Amperstrand/nucula-enclosure/output/renders/detail_keypad_bay.png

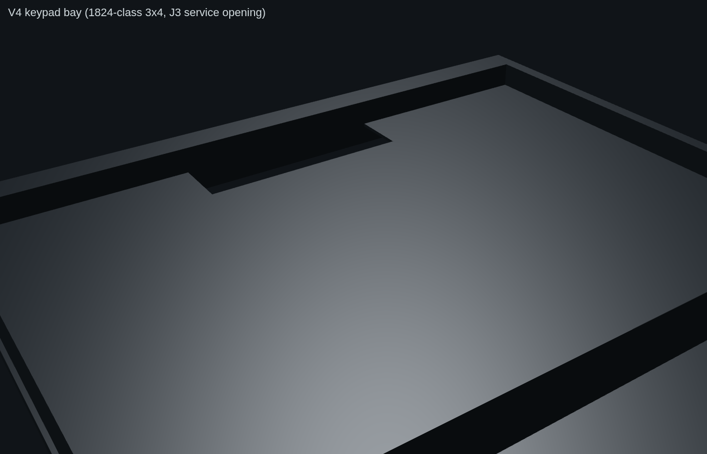
output/renders/detail_keypad_bay.png
