Amperstrand/nucula-enclosure/output/renders/detail_button_ports.png

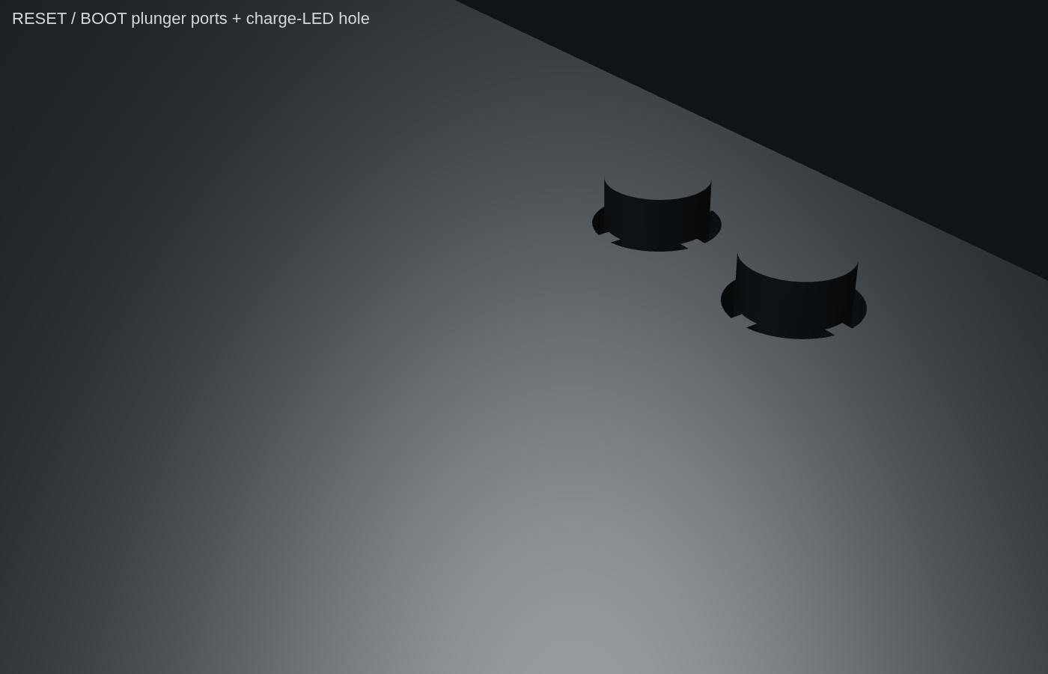
output/renders/detail_button_ports.png
