Amperstrand/nucula-enclosure/output/renders/detail_battery_pocket.png

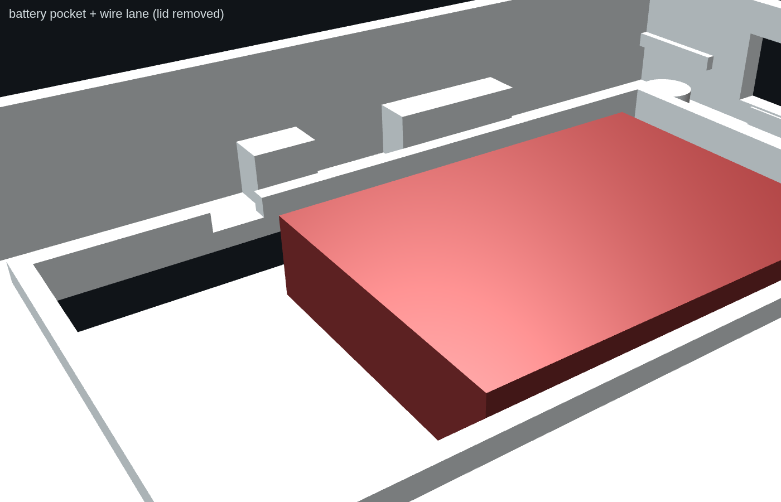
output/renders/detail_battery_pocket.png
