Amperstrand/nucula-enclosure/output/renders/detail_coupon.png

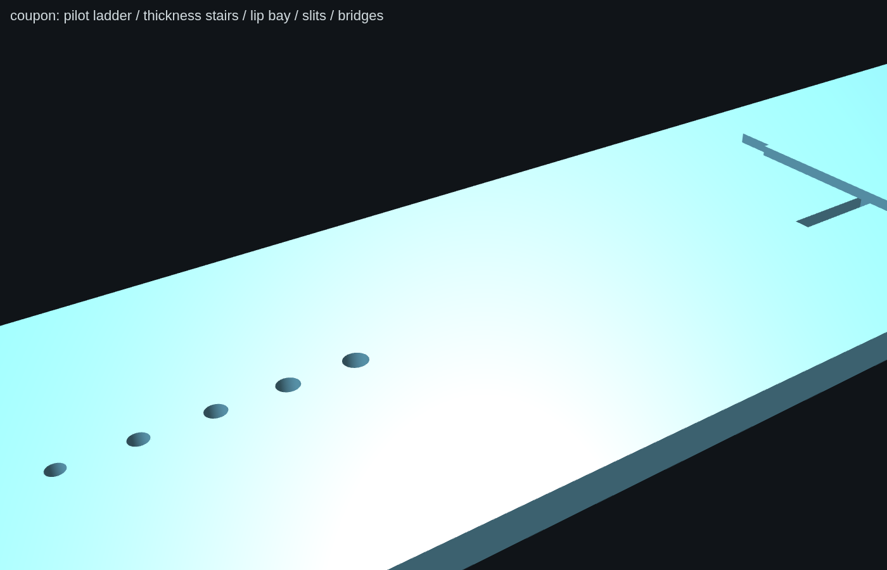
output/renders/detail_coupon.png
