Amperstrand/nucula-enclosure/output/renders/detail_popout_window.png

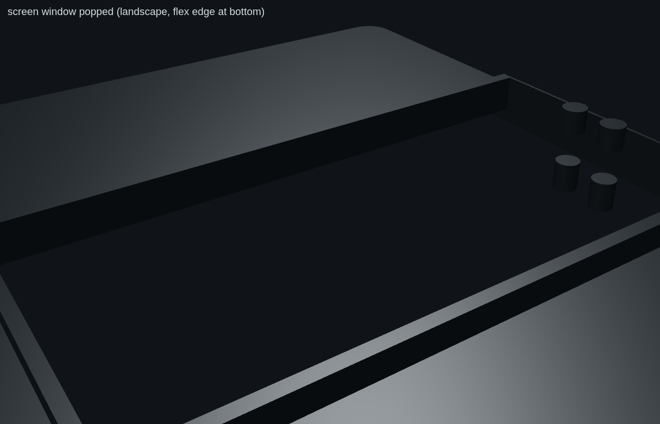
output/renders/detail_popout_window.png
