Amperstrand/nucula-enclosure/output/renders/detail_usb_battery_ports.png

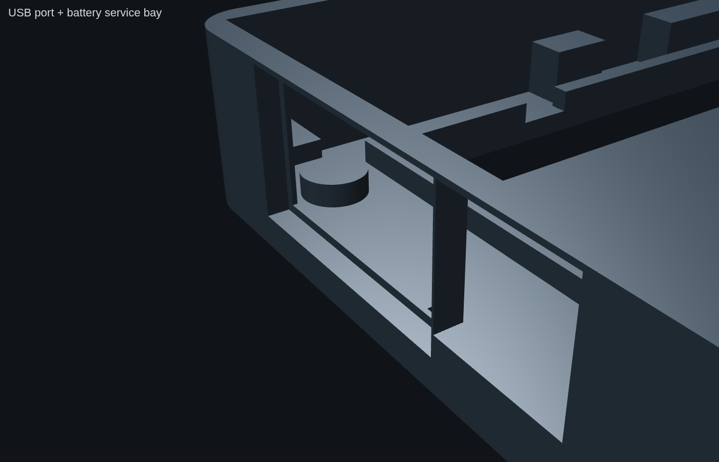
output/renders/detail_usb_battery_ports.png
