Amperstrand/nucula-enclosure/output/renders/OPTIONS_overview.png

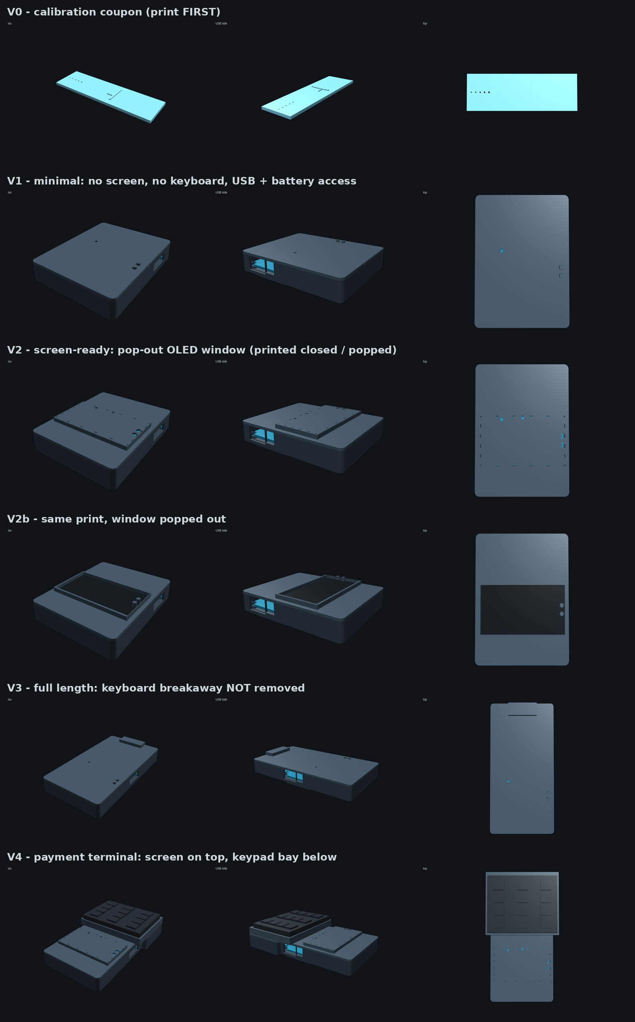
output/renders/OPTIONS_overview.png
