Amperstrand/nucula-enclosure/output/renders/V0_coupon_iso.png

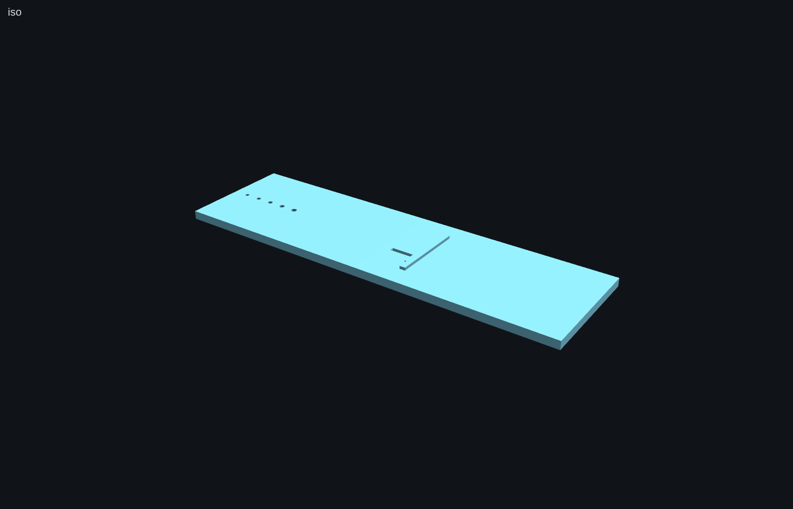
output/renders/V0_coupon_iso.png
