Amperstrand/nucula-enclosure/output/renders/V0_coupon_top.png

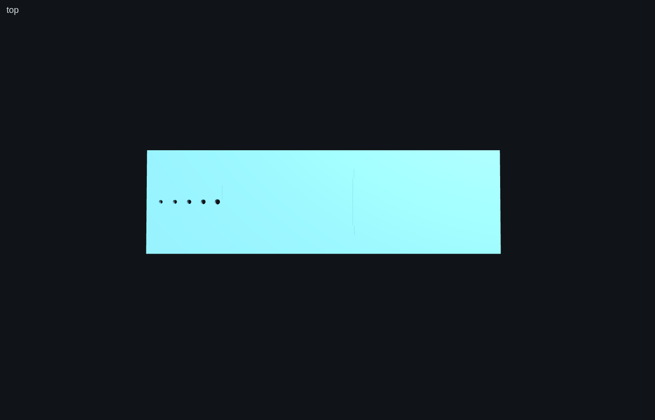
output/renders/V0_coupon_top.png
