Amperstrand/nucula-enclosure/output/renders/V0_coupon_usb.png

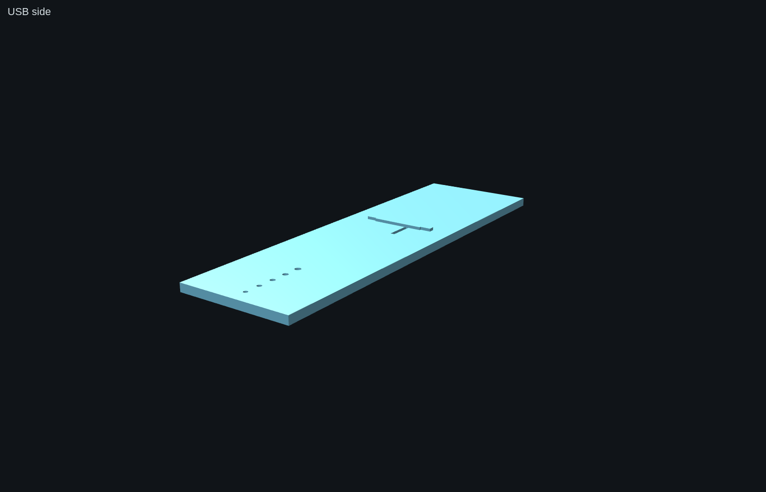
output/renders/V0_coupon_usb.png
