Amperstrand/nucula-enclosure/output/renders/V1_minimal_closed_iso.png

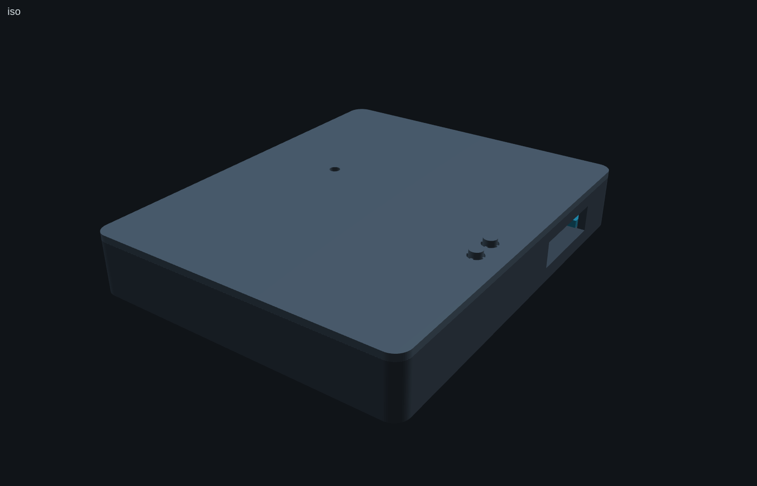
output/renders/V1_minimal_closed_iso.png
