Amperstrand/nucula-enclosure/output/renders/V1_minimal_closed_top.png

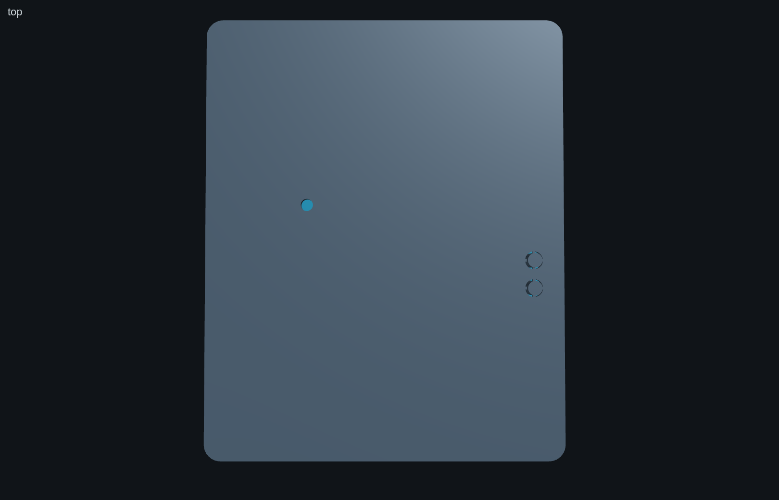
output/renders/V1_minimal_closed_top.png
