Amperstrand/nucula-enclosure/output/renders/V1_minimal_closed_usb.png

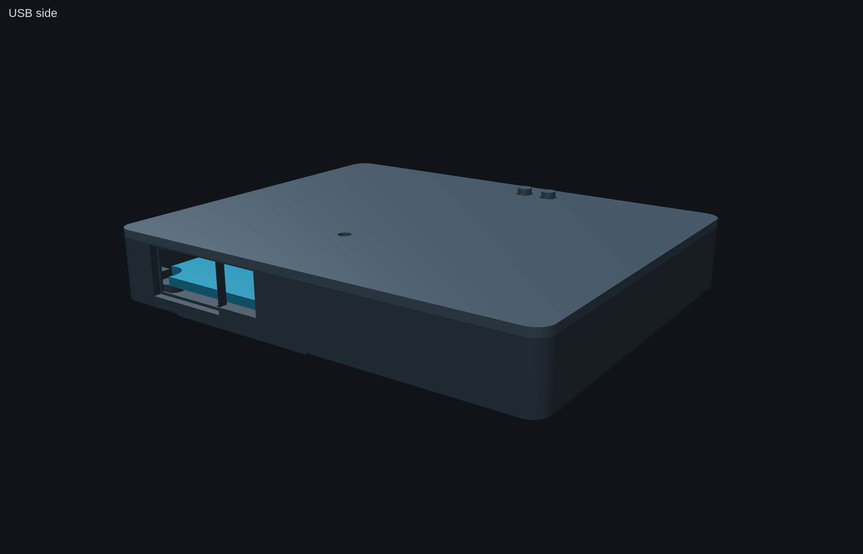
output/renders/V1_minimal_closed_usb.png
