Amperstrand/nucula-enclosure/output/renders/V2_screen_popped_iso.png

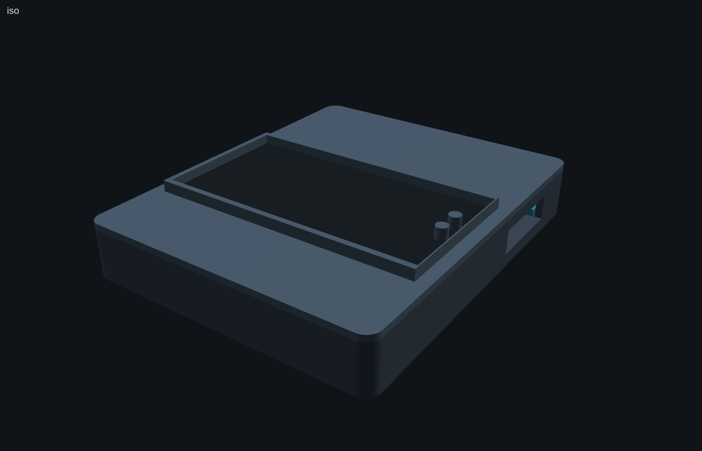
output/renders/V2_screen_popped_iso.png
