Amperstrand/nucula-enclosure/output/renders/V2_screen_popped_top.png

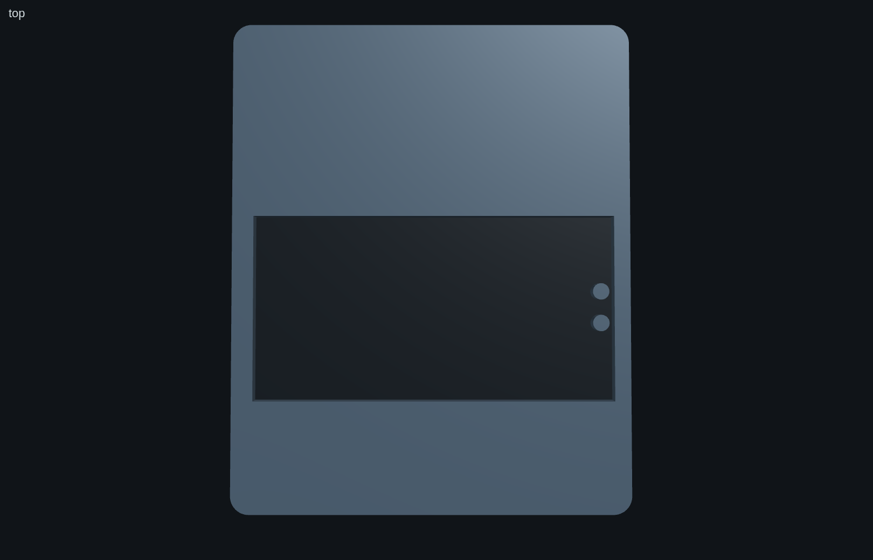
output/renders/V2_screen_popped_top.png
