Amperstrand/nucula-enclosure/output/renders/V3_full_keyboard_iso.png

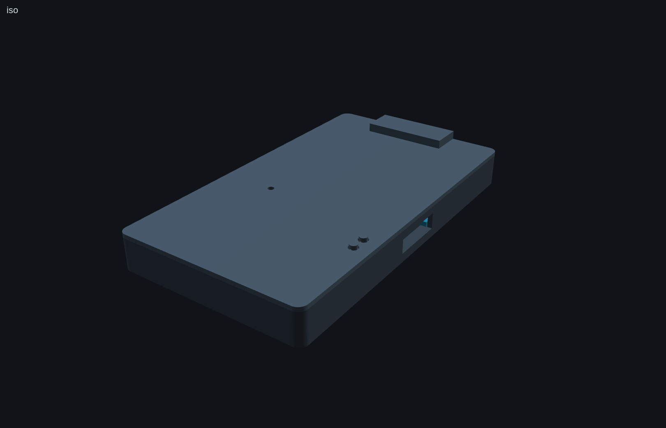
output/renders/V3_full_keyboard_iso.png
