Amperstrand/nucula-enclosure/output/renders/V3_full_keyboard_top.png

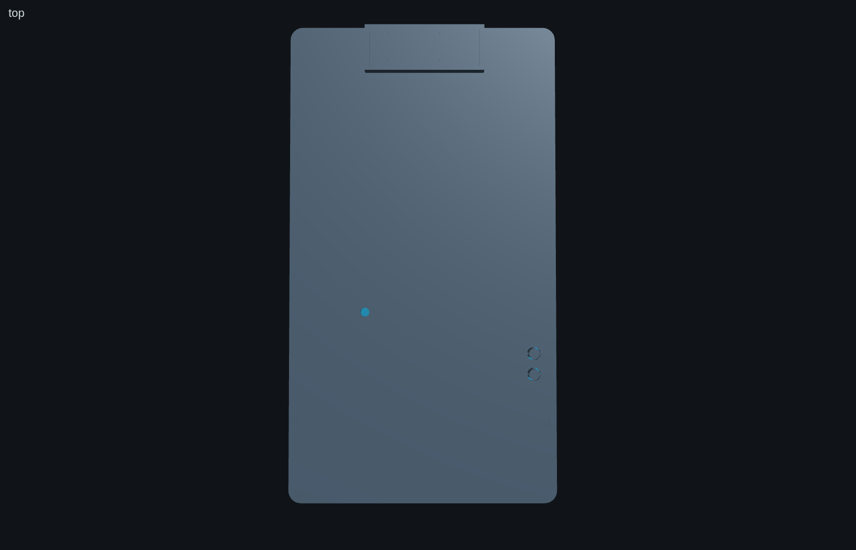
output/renders/V3_full_keyboard_top.png
