Amperstrand/nucula-enclosure/output/renders/V3_full_keyboard_usb.png

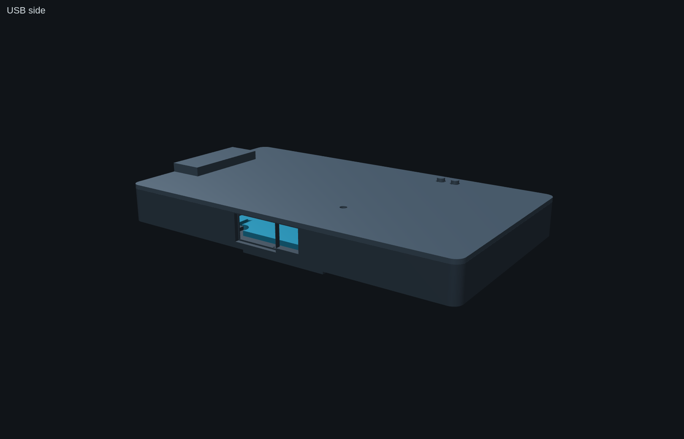
output/renders/V3_full_keyboard_usb.png
