Amperstrand/nucula-enclosure/output/renders/V4_terminal_iso.png

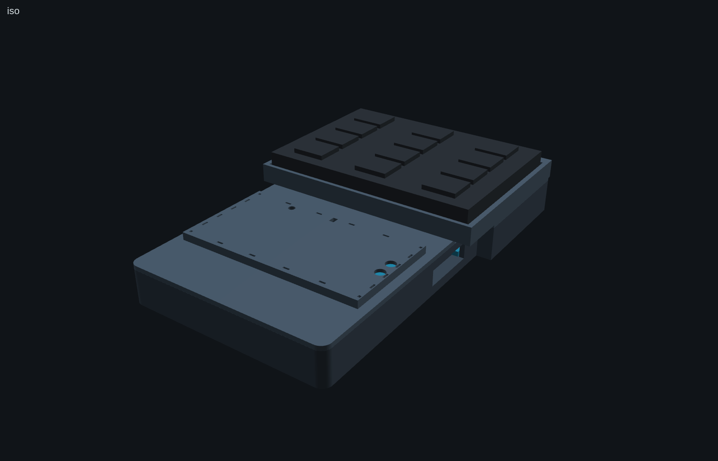
output/renders/V4_terminal_iso.png
