Amperstrand/nucula-enclosure/output/renders/V4_terminal_top.png

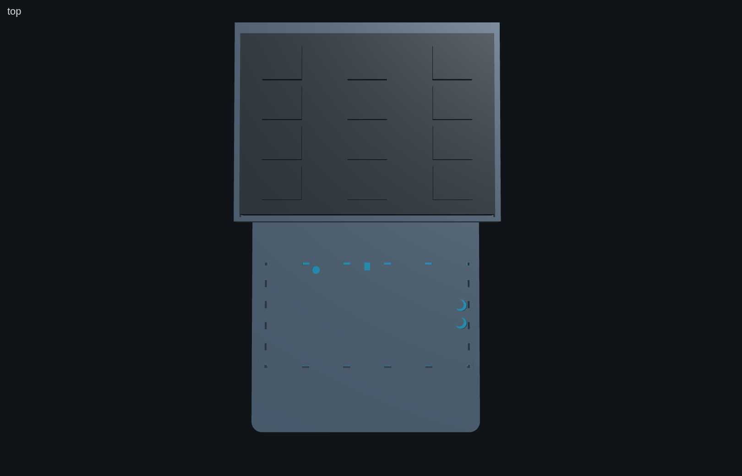
output/renders/V4_terminal_top.png
