Amperstrand/nucula-enclosure/output/renders/V4_terminal_usb.png

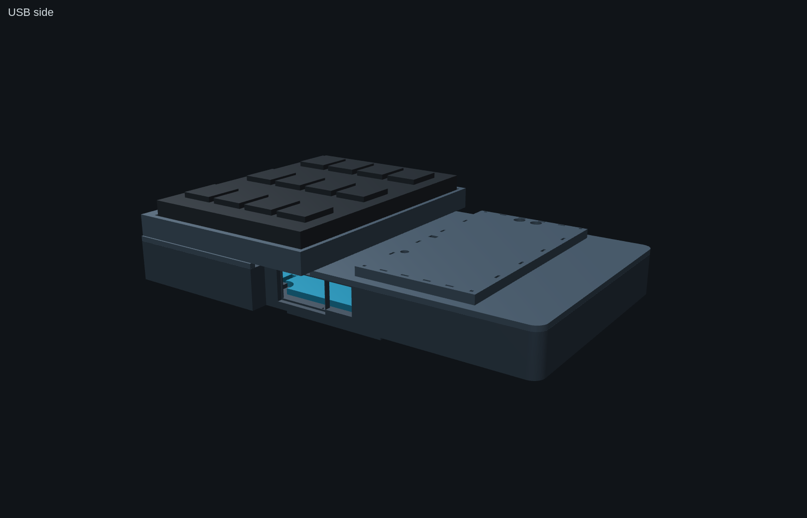
output/renders/V4_terminal_usb.png
