Amperstrand/nucula-enclosure/output/exports/battery.stl

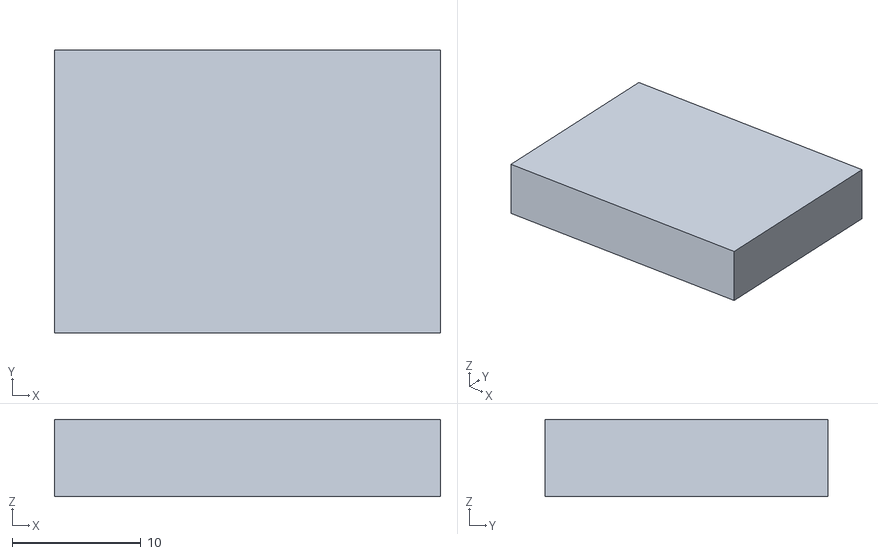
[picture p36: CAD file, 2026-10-08]
output/exports/battery.stl
30.0 x 22.0 x 6.00
